labdvm/SX1255-Tetra-TMO-HS-HAT/HAT with PA/HAT with PA_b.png

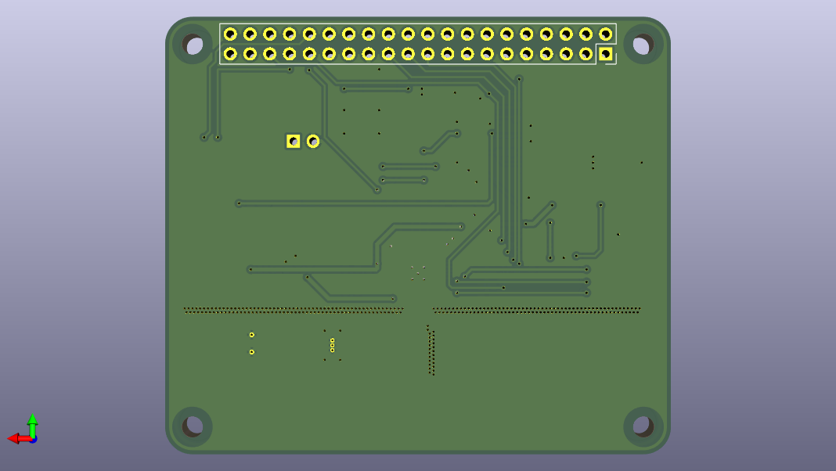
HAT with PA/HAT with PA_b.png
